LEDs-by-glowingkitty/GlowLight/images/glowlight_esp32_s3.jpg

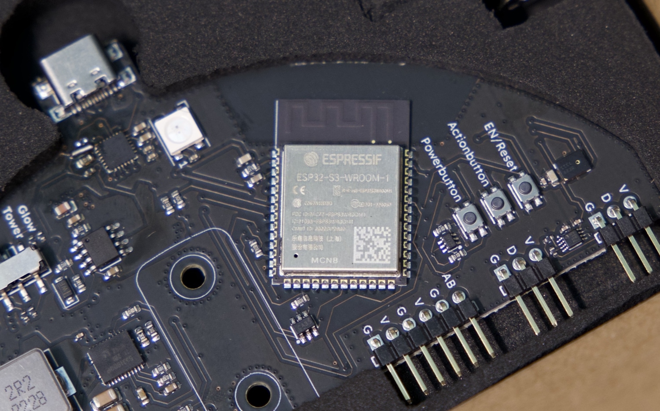
images/glowlight_esp32_s3.jpg
