LEDs-by-glowingkitty/GlowLight/images/glowlight_led_strips.jpg

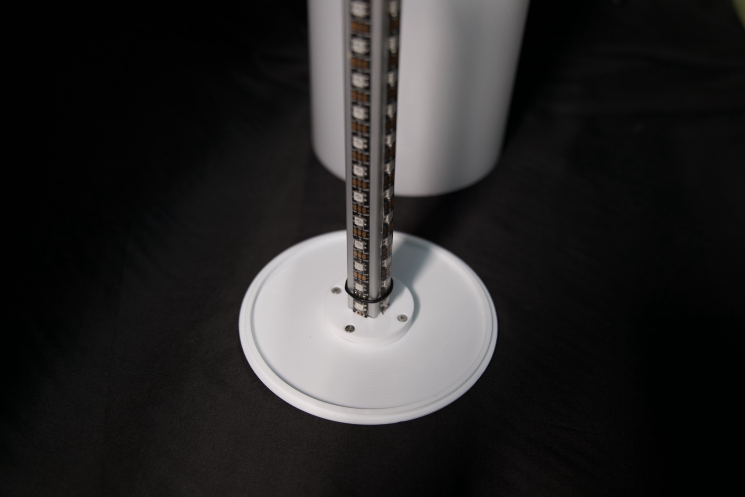
images/glowlight_led_strips.jpg
