LEDs-by-glowingkitty/GlowLight/images/glowlight_main_picture.jpg

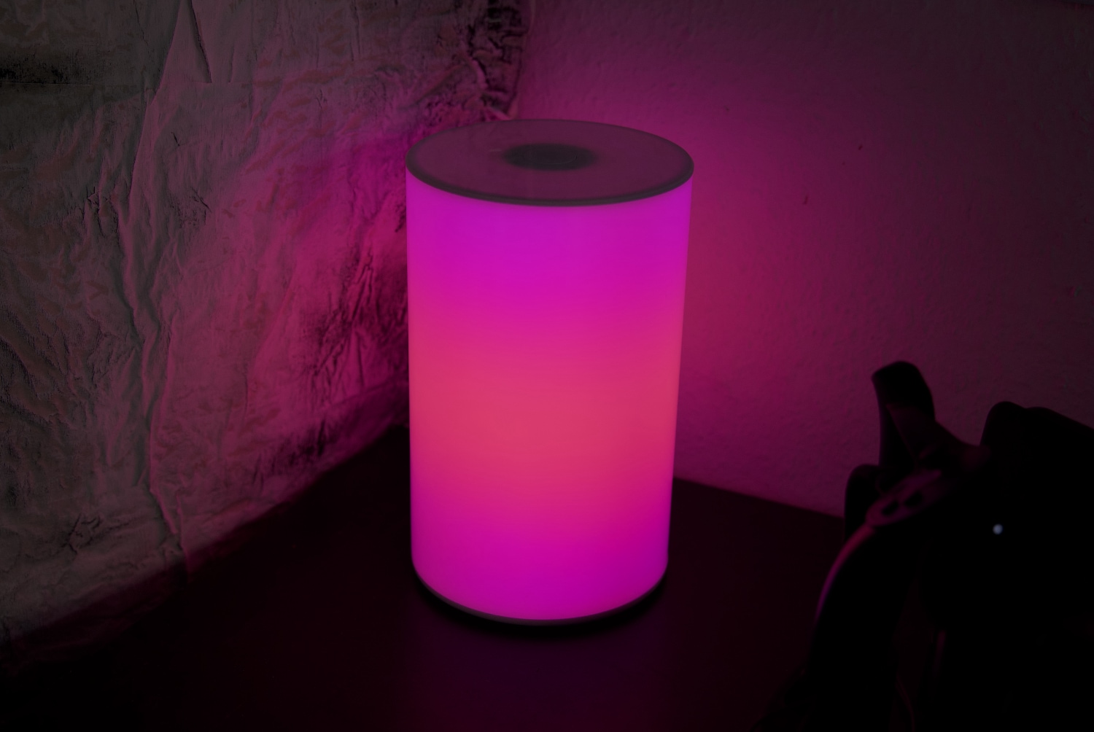
images/glowlight_main_picture.jpg
