LEDs-by-glowingkitty/GlowLight/images/glowlight_pcb.jpg

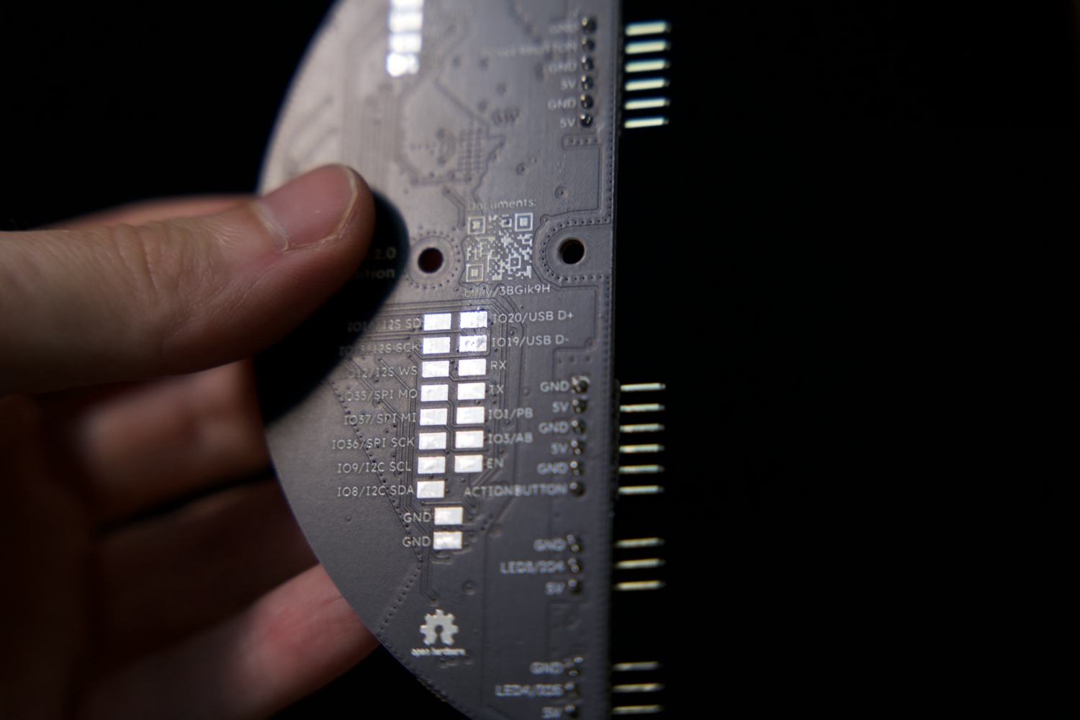
images/glowlight_pcb.jpg
