LEDs-by-glowingkitty/GlowLight/images/glowlight_white.jpg

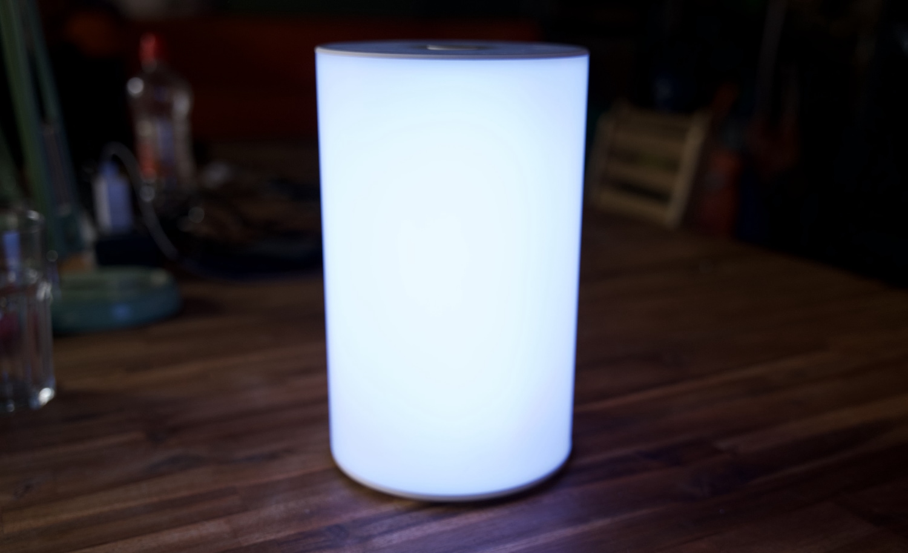
images/glowlight_white.jpg
