LEDs-by-glowingkitty/GlowLight/images/glowlightheader.jpg

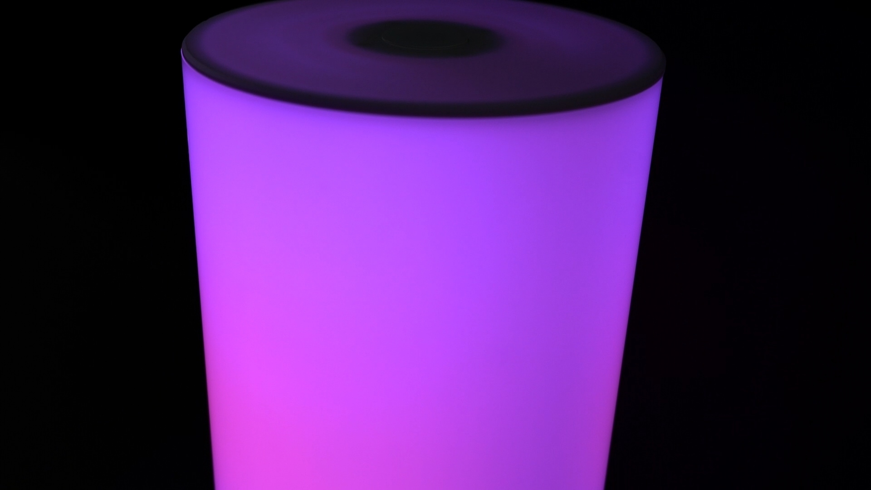
images/glowlightheader.jpg
