LEDs-by-glowingkitty/GlowLight/images/manyeffects.jpg

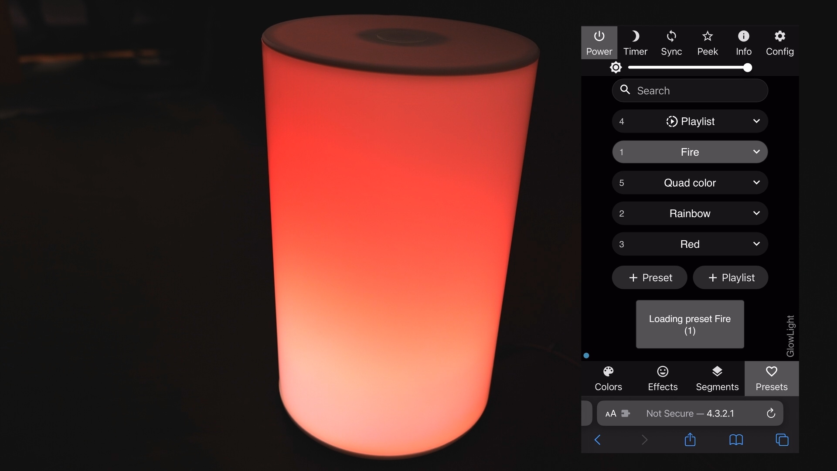
images/manyeffects.jpg
