LEDs-by-glowingkitty/GlowLight/PCB files/Button PCB/Button PCB.kicad_sch

## KiCad design PCB files/Button PCB/Button PCB.kicad_sch (2023-05-19)

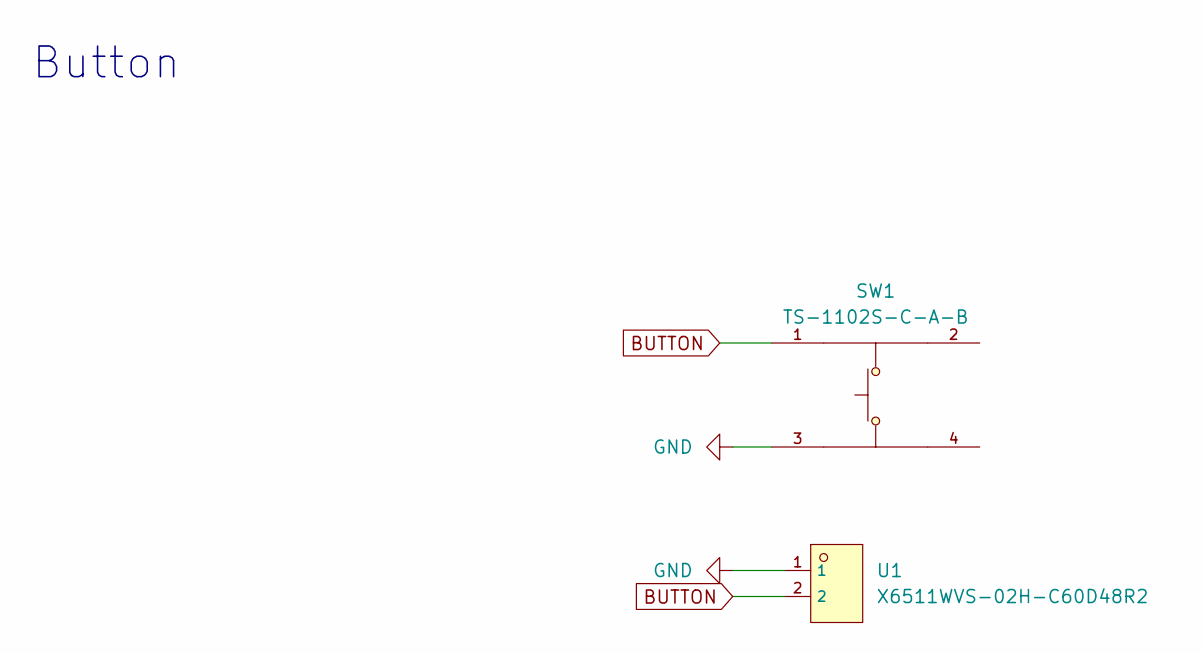
[picture p32: schematic Button PCB.kicad_sch]

Parts:
SW1: TS-1102S-C-A-B; KEY-SMD_4P-L6.0-W6.0-P4.50-LS8.6; LCSC # C381038
U1: X6511WVS-02H-C60D48R2; HDR-SMD_2P-P2.54_XKB_X6511WVS-02H-C60D48R2; LCSC C2883759

Connections:
BUTTON: SW1.1, U1.2
GND: SW1.3, U1.1

Notes on the sheet:
Button
