LEDs-by-glowingkitty/GlowLight/PCB files/MainPCB/MainPCB.kicad_sch

## KiCad design PCB files/MainPCB/MainPCB.kicad_sch (2023-12-09, an earlier design)

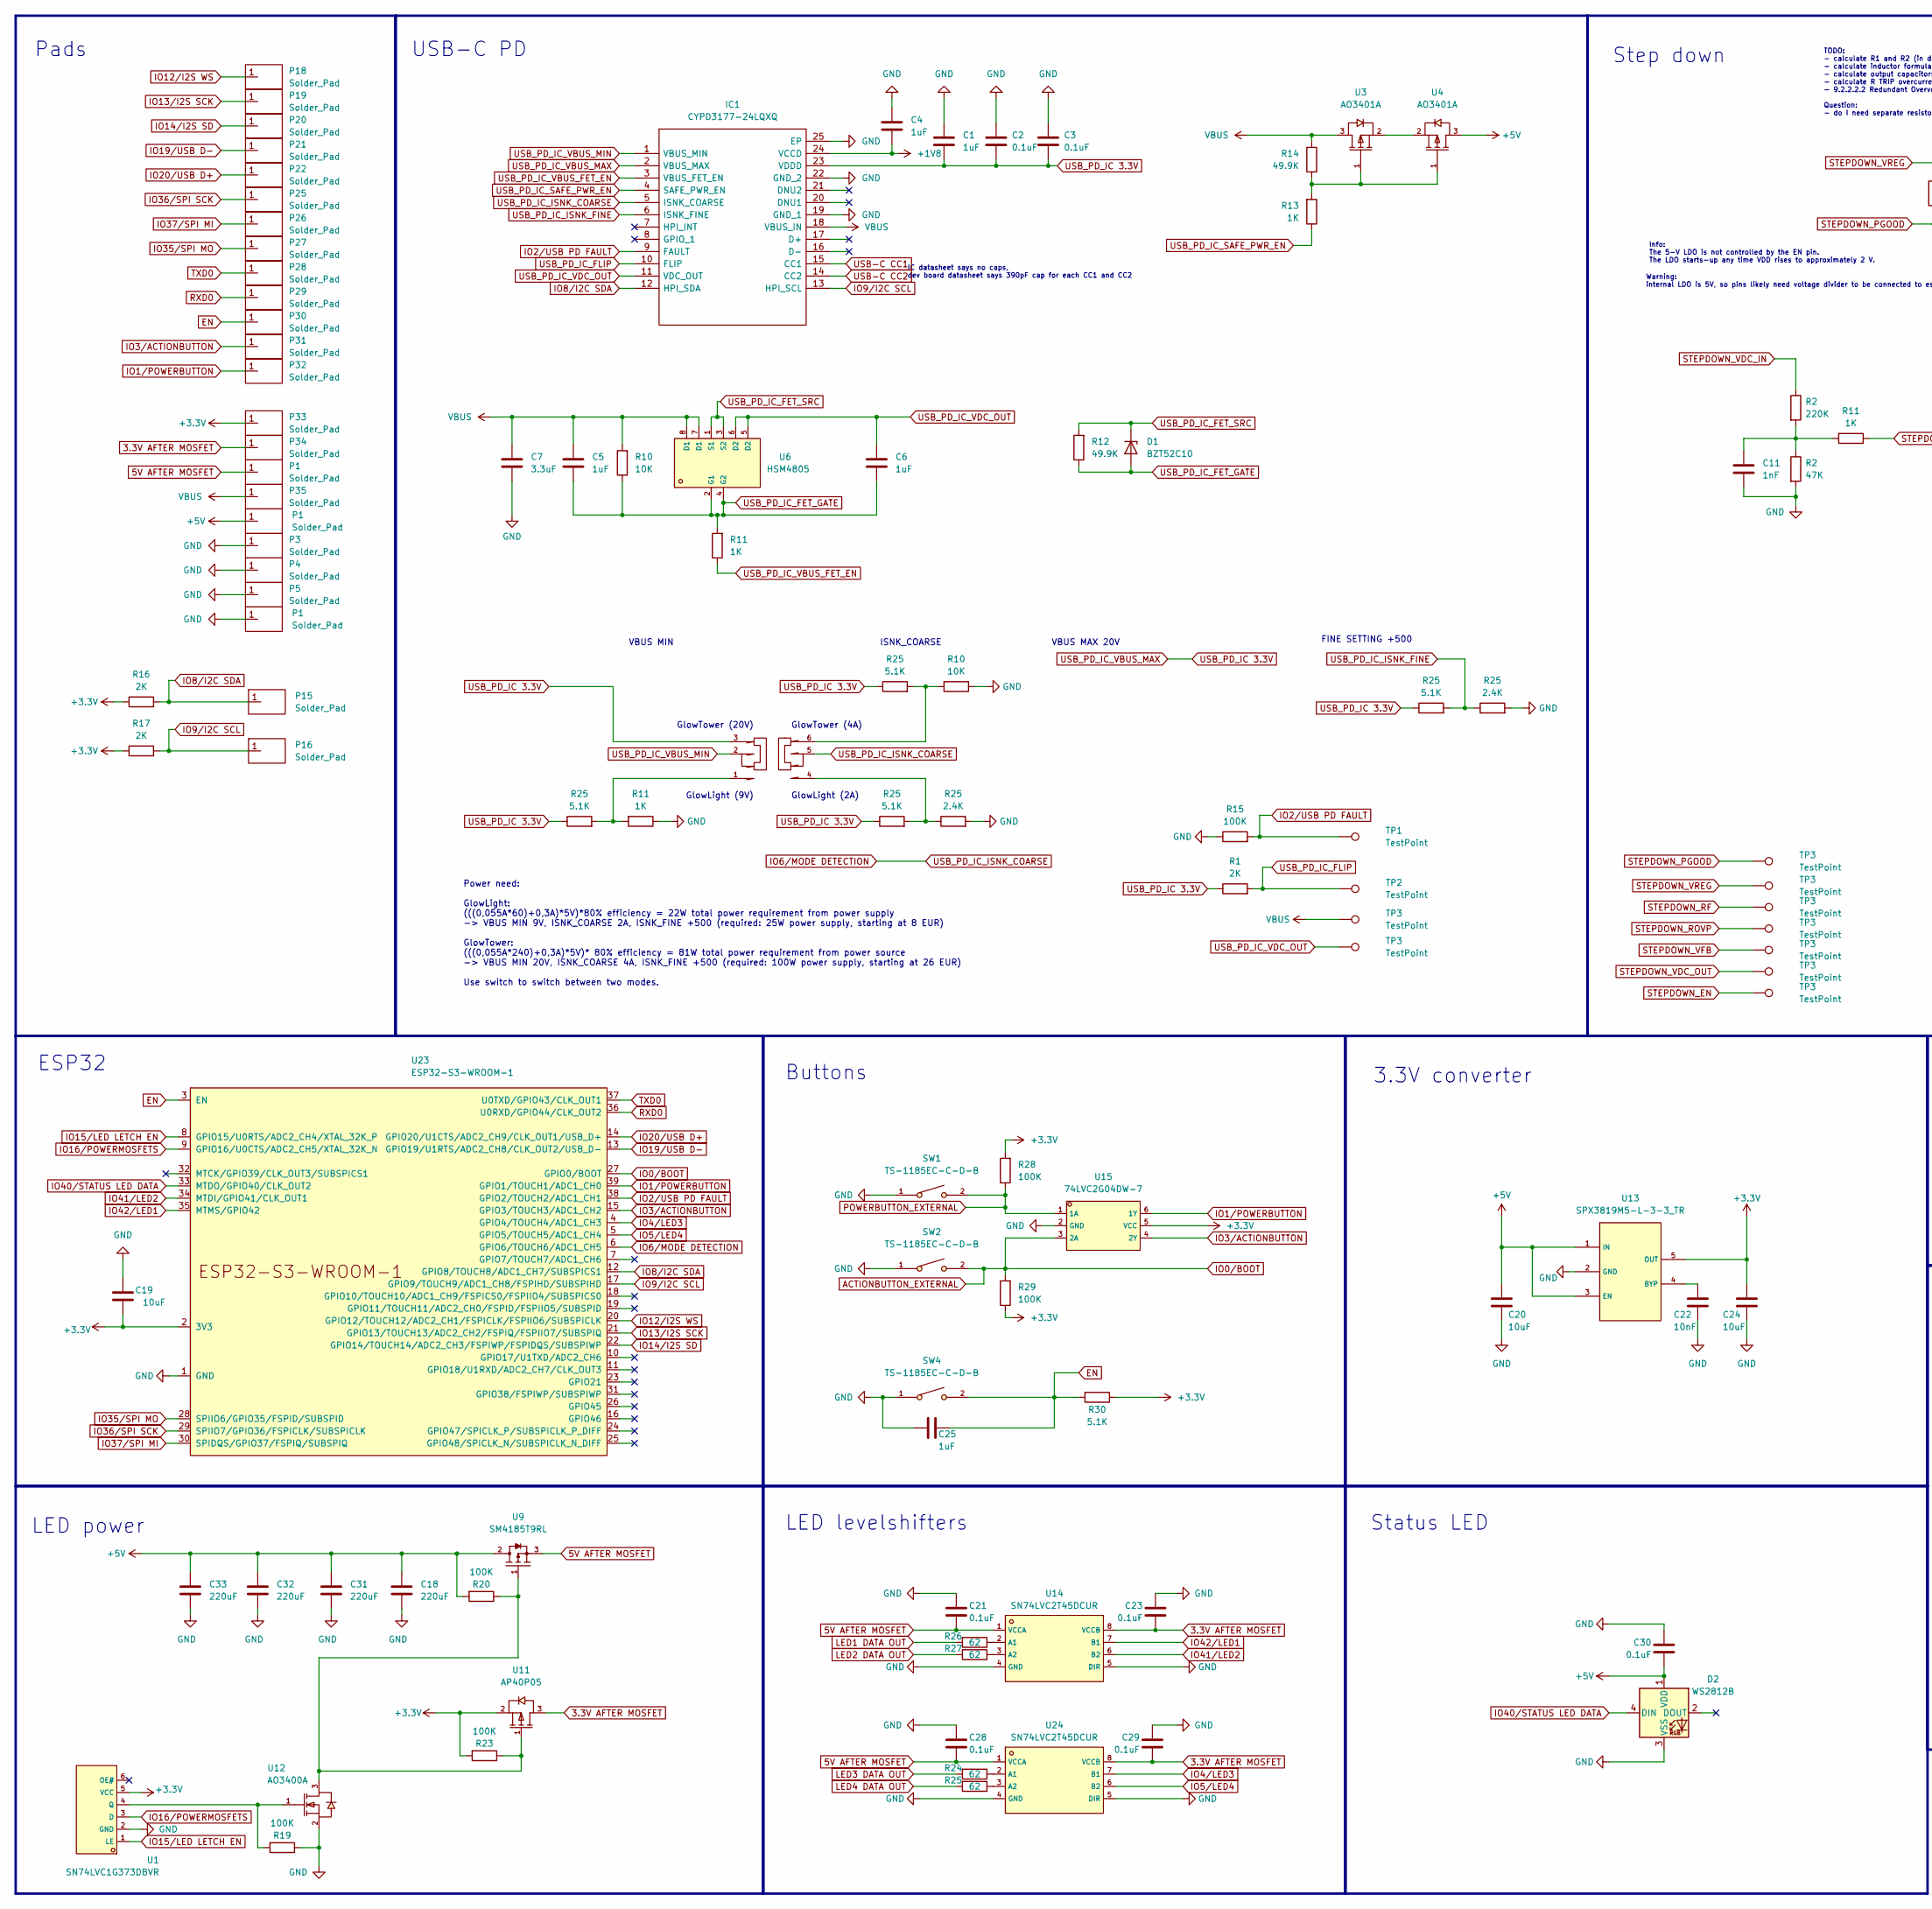
[picture p33: schematic MainPCB.kicad_sch, part in row 1, column 1]

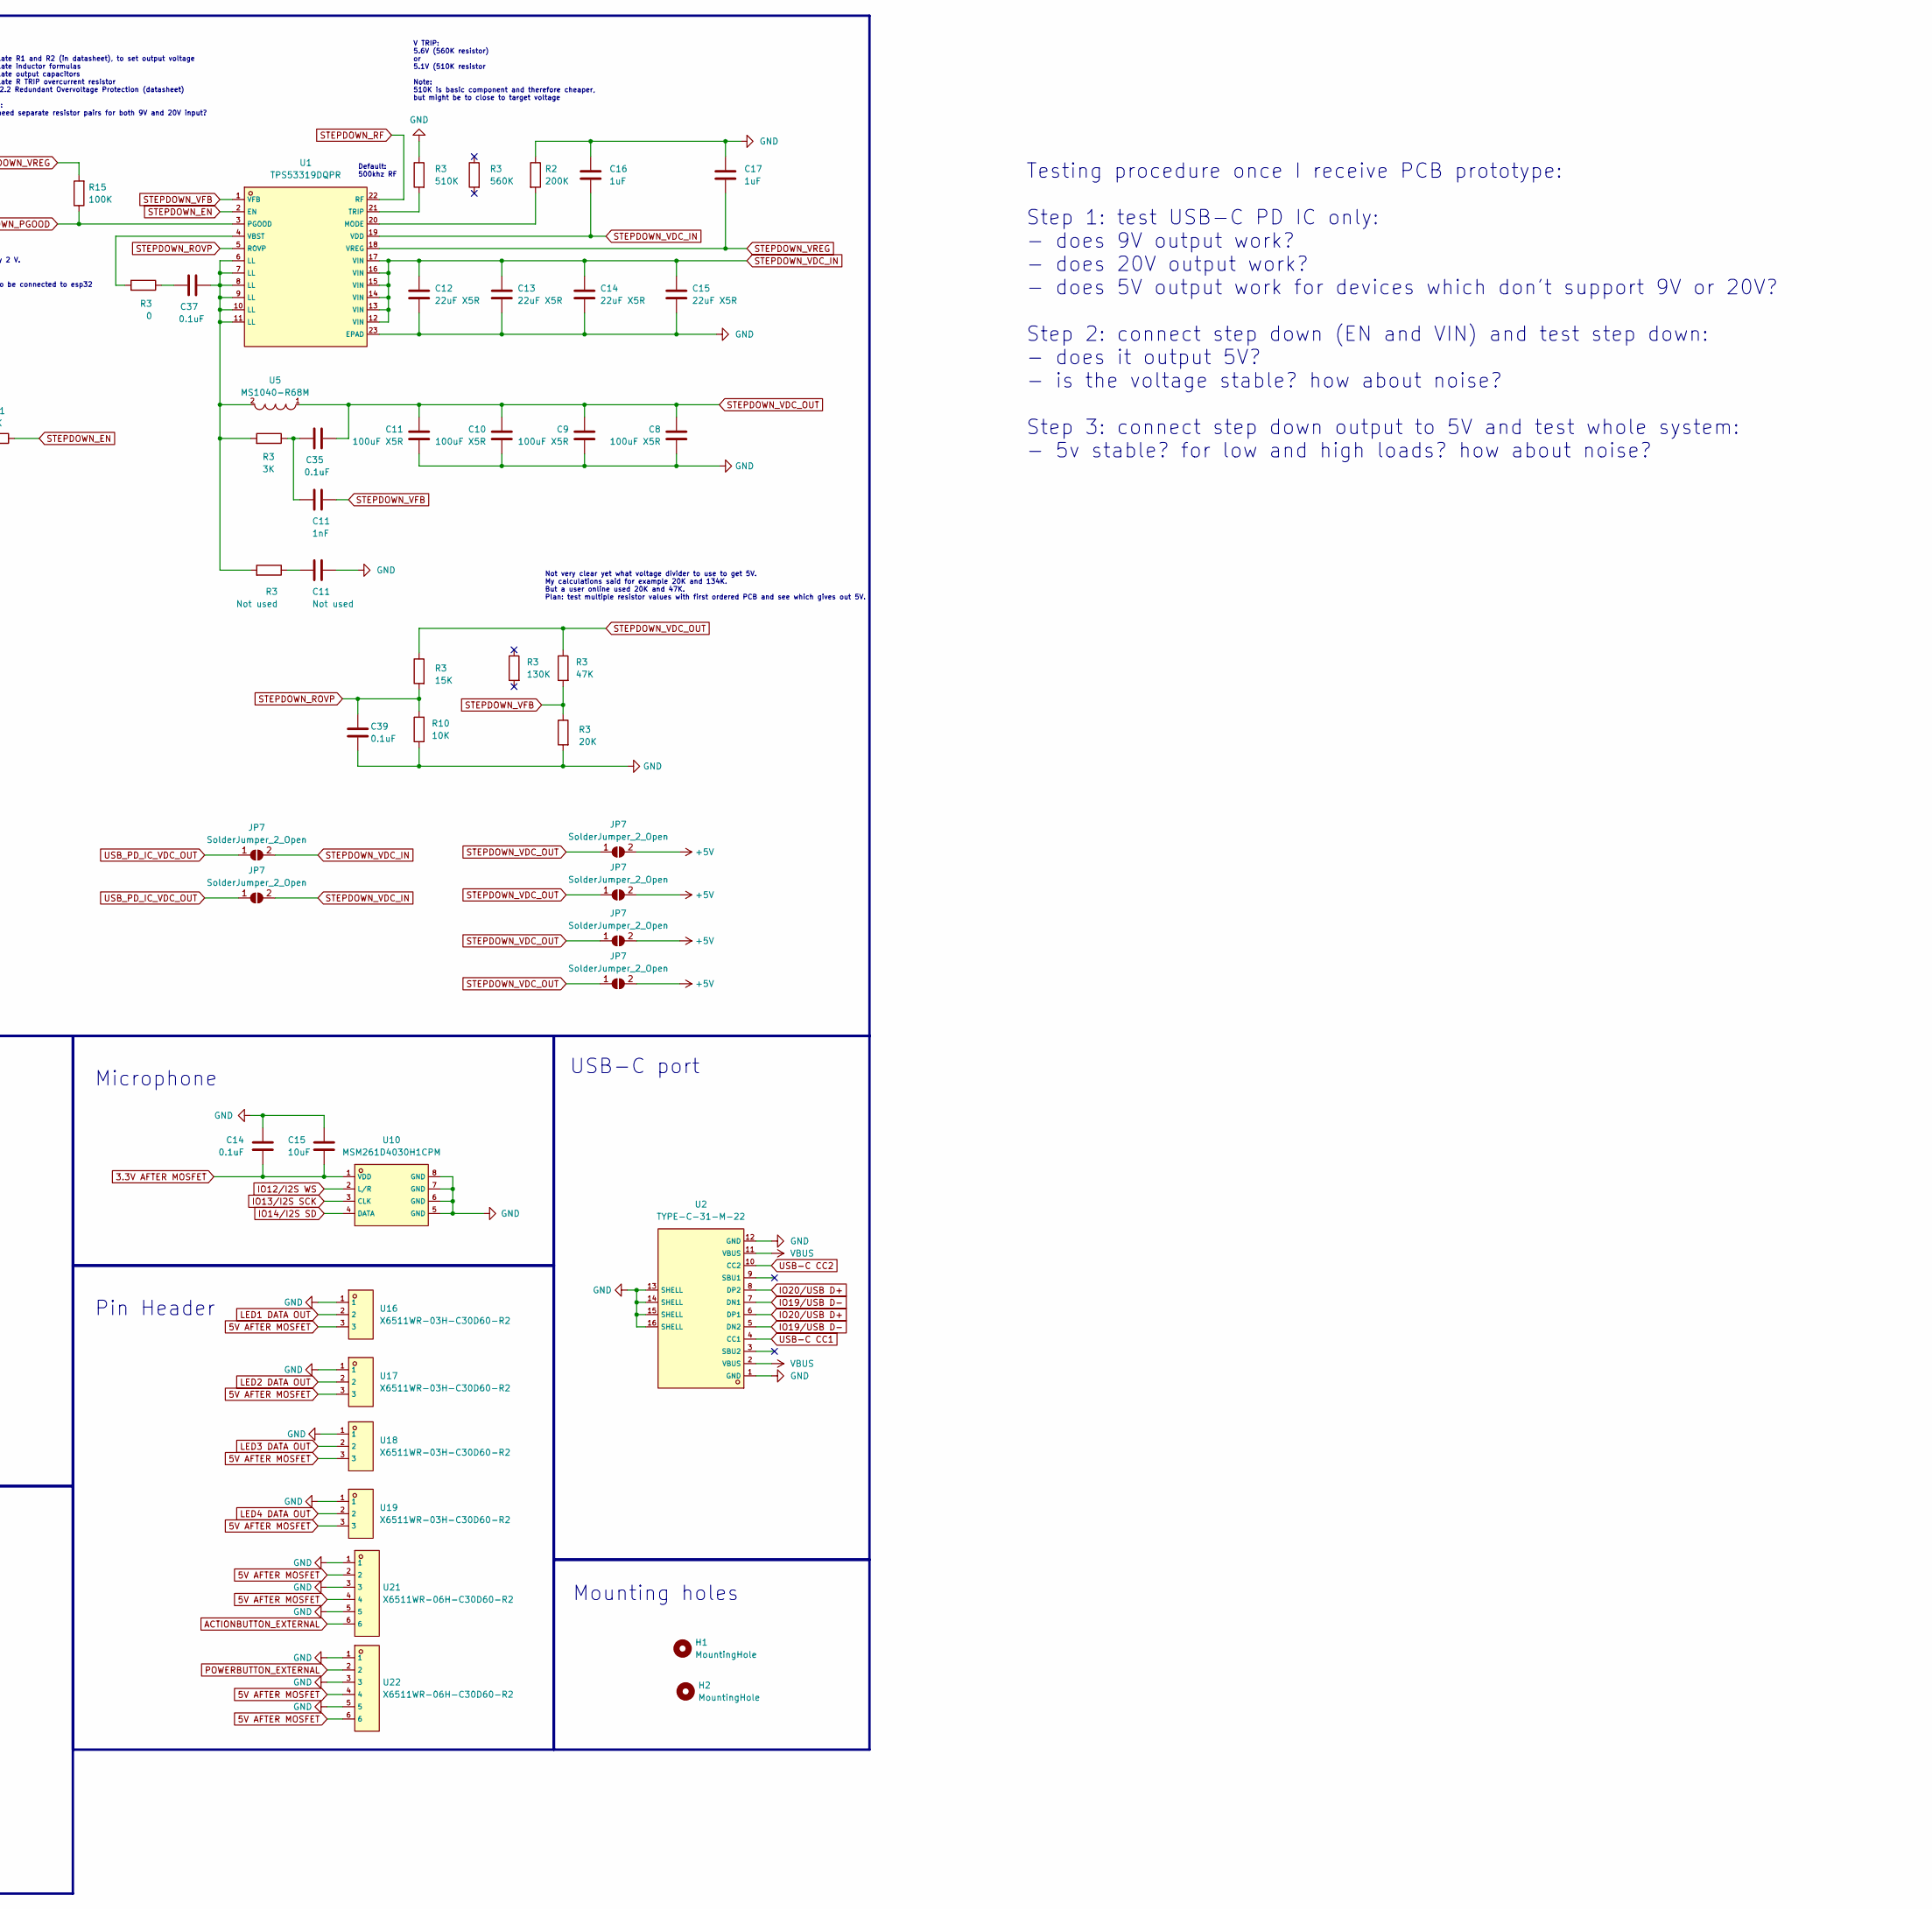
[picture p34: schematic MainPCB.kicad_sch, part in row 1, column 2]

Parts:
C1, C4, C5, C6, C16, C17, C25: 1uF; C_0603_1608Metric; LCSC # C15849
C2, C3, C14, C21, C23, C28, C29, C30, C35, C37, C39: 0.1uF; C_0402_1005Metric; LCSC # C307331
C7: 3.3uF; C_0805_2012Metric; LCSC # C342775
C8, C9, C10: 100uF X5R; C_1206_3216Metric; LCSC # C15008
C11: 1nF; C_0402_1005Metric; LCSC # C1523
C12, C13: 22uF X5R; C_1206_3216Metric; LCSC # C12891
C15, C19, C20, C24: 10uF; C_0603_1608Metric; LCSC # C96446
C18, C31, C32, C33: 220uF; C_1206_3216Metric; LCSC # C412252
C22: 10nF; C_0402_1005Metric; LCSC # C15195
D1: BZT52C10; D_SOD-123F; LCSC # C2891778
D2: WS2812B; LED_WS2812B_PLCC4_5.0x5.0mm_P3.2mm; LCSC # C2843785
H1, H2: MountingHole; MountingHole_3.2mm_M3
IC1: CYPD3177-24LQXQ; RT9471_vias_in_pad; LCSC # C2959321
JP7: SolderJumper_2_Open; SolderJumper-2_P1.3mm_Open_RoundedPad1.0x1.5mm
P1, P3, P4, P5, P15, P16, P18, P19, P20, P21, P22, P25, P26, P27, P28, P29, P30, P31, P32, P33, P34, P35: Solder_Pad; Solder pad
R1, R16, R17: 2K; R_0603_1608Metric; LCSC # C22975
R2: 200K; R_0603_1608Metric; LCSC # C25811
R3: Not used; R_0603_1608Metric
R10: 10K; R_0603_1608Metric; LCSC # C25804
R11, R13: 1K; R_0603_1608Metric; LCSC # C21190
R12, R14: 49.9K; R_0603_1608Metric; LCSC # C23184
R15, R19, R20, R23, R28, R29: 100K; R_0603_1608Metric; LCSC # C25803
R24, R26, R27: 62; R_0402_1005Metric; LCSC # C4962
R25: 2.4K; R_0603_1608Metric; LCSC # C22940
R30: 5.1K; R_0603_1608Metric; LCSC # C23186
SW1, SW2, SW4: TS-1185EC-C-D-B; SW-SMD_4P-L3.7-W3.0-P1.50-LS4.7; LCSC # C318893
SW3: SK-3245S-L3-B; SW-SMD_SK-3245S-L3-B; LCSC # C405954
TP1, TP2, TP3: TestPoint; TestPoint_Pad_D1.5mm
U1: TPS53319DQPR; LSON-CLIP-22_L6.0-W5.0-P0.50-BL-EP; LCSC # C181971
U2: TYPE-C-31-M-22; USB-C-SMD_TYPE-C-31-M-22; LCSC # C530612
U3, U4: AO3401A; SOT-23_L2.9-W1.3-P1.90-LS2.4-BR; LCSC # C15127
U5: MS1040-R68M; IND-SMD_L11.5-W10.0_MCF-1050; LCSC # C380043
U6: HSM4805; SOP-8_L4.9-W3.9-P1.27-LS6.0-BL; LCSC # C700973
U9: SM4185T9RL; TO-252-2_L6.6-W6.1-P4.57-LS10.1-BL-1; LCSC # C5143535
U10: MSM261D4030H1CPM; MIC-SMD_8P-L4.0-W3.0_ZTS6231; LCSC # C966942
U11: AP40P05; SOT-23-3_L2.9-W1.3-P1.90-LS2.4-BR; LCSC # C2886385
U12: AO3400A; SOT-23-3_L2.9-W1.6-P1.90-LS2.8-BR; LCSC # C20917
U13: SPX3819M5-L-3-3_TR; SOT-23-5_L3.0-W1.7-P0.95-LS2.8-BR; LCSC # C9055
U14, U24: SN74LVC2T45DCUR; VSSOP-8_L2.4-W2.1-P0.50-LS3.2-BR; LCSC # C15741
U15: 74LVC2G04DW-7; SOT-363_L2.0-W1.3-P0.65-LS2.1-BR; LCSC # C69053
U16, U17, U18, U19: X6511WR-03H-C30D60-R2; HDR-TH_3P-P2.54-H-M-W10.4; LCSC # C706866
U21, U22: X6511WR-06H-C30D60-R2; HDR-TH_6P-P2.54-H-M-W10.4; LCSC # C706869
U23: ESP32-S3-WROOM-1; LCSC # C2913197

Connections:
3.3V AFTER MOSFET: C14.2, C15.2, C23.2, C29.2, P34.1, U10.1 (VDD), U11.3 (D), U14.8 (VCCB), U24.8 (VCCB)
5V AFTER MOSFET: C21.2, C28.2, P1.1, U9.3 (S), U14.1 (VCCA), U16.3, U17.3, U18.3, U19.3, U21.2, U21.4, U22.4, U22.6, U24.1 (VCCA)
+1V8: C4.2, IC1.24 (VCCD)
+3.3V: C19.2, C24.2, P33.1, R16.1, R17.1, R23.2, R28.2, R29.1, R30.1, U1.5 (VCC), U11.2 (S), U13.5 (OUT), U15.5 (VCC), U23.2 (3V3)
+5V: C18.1, C20.2, C30.2, C31.1, C32.1, C33.1, D2.1 (VDD), JP7.2 (B), P1.1, R20.2, U4.3 (D), U9.2 (D), U13.1 (IN), U13.3 (EN)
ACTIONBUTTON_EXTERNAL: R29.2, SW2.2, U15.3 (2A), U21.6, U23.27 (GPIO0/BOOT)
EN: C25.2, P30.1, R30.2, SW4.2, U23.3 (EN)
GND: C1.1, C2.1, C3.1, C4.1, C7.1, C8.2, C9.2, C10.2, C11.1, C11.2, C12.2, C13.2, C14.1, C14.2, C15.1, C15.2, C16.1, C17.1, C18.2, C19.1, C20.1, C21.1, C22.1, C23.1, C24.1, C25.1, C28.1, C29.1, C30.1, C31.2, C32.2, C33.2, C39.2, D2.3 (VSS), IC1.19 (GND_1), IC1.22 (GND_2), IC1.25 (EP), P1.1, P3.1, P4.1, P5.1, R2.1, R2.2, R3.1, R3.2, R10.1, R11.1, R15.1, R19.1, R25.2, SW1.1, SW2.1, SW4.1, U1.2 (GND), U1.23 (EPAD), U2.1 (GND), U2.12 (GND), U2.13 (SHELL), U2.14 (SHELL), U2.15 (SHELL), U2.16 (SHELL), U10.5 (GND), U10.6 (GND), U10.7 (GND), U10.8 (GND), U12.2 (S), U13.2 (GND), U14.4 (GND), U14.5 (DIR), U15.2 (GND), U16.1, U17.1, U18.1, U19.1, U21.1, U21.3, U21.5, U22.1, U22.3, U22.5, U23.1 (GND), U23.40 (GND), U23.41 (GND), U24.4 (GND), U24.5 (DIR)
IO1/POWERBUTTON: P32.1, U15.6 (1Y), U23.39 (GPIO1/TOUCH1/ADC1_CH0)
IO2/USB PD FAULT: IC1.9 (FAULT), R15.2, TP1.1, U23.38 (GPIO2/TOUCH2/ADC1_CH1)
IO3/ACTIONBUTTON: P31.1, U15.4 (2Y), U23.15 (GPIO3/TOUCH3/ADC1_CH2)
IO4/LED3: U23.4 (GPIO4/TOUCH4/ADC1_CH3), U24.7 (B1)
IO5/LED4: U23.5 (GPIO5/TOUCH5/ADC1_CH4), U24.6 (B2)
IO6/MODE DETECTION: IC1.5 (ISNK_COARSE), SW3.5, U23.6 (GPIO6/TOUCH6/ADC1_CH5)
IO8/I2C SDA: IC1.12 (HPI_SDA), P15.1, R16.2, U23.12 (GPIO8/TOUCH8/ADC1_CH7/SUBSPICS1)
IO9/I2C SCL: IC1.13 (HPI_SCL), P16.1, R17.2, U23.17 (GPIO9/TOUCH9/ADC1_CH8/FSPIHD/SUBSPIHD)
IO12/I2S WS: P18.1, U10.2 (L/R), U23.20 (GPIO12/TOUCH12/ADC2_CH1/FSPICLK/FSPIIO6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)
IO13/I2S SCK: P19.1, U10.3 (CLK), U23.21 (GPIO13/TOUCH13/ADC2_CH2/FSPIQ/FSPIIO7/S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)
IO14/I2S SD: P20.1, U10.4 (DATA), U23.22 (GPIO14/TOUCH14/ADC2_CH3/FSPIWP/FSPIDQS/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)
IO15/LED LETCH EN: U1.1 (LE), U23.8 (GPIO15/U0RTS/ADC2_CH4/XTAL_32K_P)
IO16/POWERMOSFETS: U1.3 (D), U23.9 (GPIO16/U0CTS/ADC2_CH5/XTAL_32K_N)
IO19/USB D-: P21.1, U2.5 (DN2), U2.7 (DN1), U23.13 (GPIO19/U1RTS/ADC2_CH8/CLK_OUT2/USB_D-)
IO20/USB D+: P22.1, U2.6 (DP1), U2.8 (DP2), U23.14 (GPIO20/U1CTS/ADC2_CH9/CLK_OUT1/USB_D+)
IO35/SPI MO: P27.1, U23.28 (SPIIO6/GPIO35/FSPID/SUBSPID)
IO36/SPI SCK: P25.1, U23.29 (SPIIO7/GPIO36/FSPICLK/SUBSPICLK)
IO37/SPI MI: P26.1, U23.30 (SPIDQS/GPIO37/FSPIQ/SUBSPIQ)
IO40/STATUS LED DATA: D2.4 (DIN), U23.33 (MTDO/GPIO40/CLK_OUT2)
IO41/LED2: U14.6 (B2), U23.34 (MTDI/GPIO41/CLK_OUT1)
IO42/LED1: U14.7 (B1), U23.35 (MTMS/GPIO42)
LED1 DATA OUT: R26.2, U16.2
LED2 DATA OUT: R27.2, U17.2
LED3 DATA OUT: R24.2, U18.2
LED4 DATA OUT: R25.2, U19.2
unnamed: C11.1, R2.1, R2.2, R11.2
unnamed: C11.2, C35.1, R3.1
unnamed: C22.2, U13.4 (BYP)
unnamed: C37.1, R3.1
unnamed: C37.2, R3.2, U1.6 (OE#), U1.7 (LL), U1.8 (LL), U1.9 (LL), U1.10 (LL), U1.11 (LL), U5.2
unnamed: R2.2, U1.20 (MODE)
unnamed: R3.2, U1.4 (Q), U1.21 (TRIP)
unnamed: R10.2, R25.2, SW3.6
unnamed: R11.2, R25.2, SW3.1
unnamed: R13.2, R14.1, U3.1 (G), U4.1 (G)
unnamed: R19.2, U1.4 (Q), U12.1 (G)
unnamed: R20.1, R23.1, U9.1 (G), U11.1 (G), U12.3 (D)
unnamed: R24.1, U24.2 (A1)
unnamed: R25.1, R25.2, SW3.4, U24.3 (A2)
unnamed: R26.1, U14.2 (A1)
unnamed: R27.1, U14.3 (A2)
unnamed: U3.2 (S), U4.2 (S)
POWERBUTTON_EXTERNAL: R28.1, SW1.2, U15.1 (1A), U22.2
RXD0: P29.1, U23.36 (U0RXD/GPIO44/CLK_OUT2)
STEPDOWN_EN: R11.1, TP3.1, U1.2 (GND)
STEPDOWN_PGOOD: R15.1, TP3.1, U1.3 (D)
STEPDOWN_RF: TP3.1, U1.22 (RF)
STEPDOWN_ROVP: C39.1, R3.2, R10.2, TP3.1, U1.5 (VCC)
STEPDOWN_VDC_IN: C12.1, C13.1, C14.1, C15.1, C16.2, JP7.2 (B), R2.1, U1.12 (VIN), U1.13 (VIN), U1.14 (VIN), U1.15 (VIN), U1.16 (VIN), U1.17 (VIN), U1.19 (VDD)
STEPDOWN_VDC_OUT: C8.1, C9.1, C10.1, C11.1, C35.2, JP7.1 (A), R3.1, TP3.1, U5.1
STEPDOWN_VFB: C11.1, R3.1, R3.2, TP3.1, U1.1 (LE)
STEPDOWN_VREG: C17.2, R15.2, TP3.1, U1.18 (VREG)
TXD0: P28.1, U23.37 (U0TXD/GPIO43/CLK_OUT1)
USB-C CC1: IC1.15 (CC1), U2.4 (CC1)
USB-C CC2: IC1.14 (CC2), U2.10 (CC2)
USB_PD_IC 3.3V: C1.2, C2.2, C3.2, IC1.2 (VBUS_MAX), IC1.23 (VDDD), R1.1, R25.1, SW3.3
USB_PD_IC_FET_GATE: C5.2, C6.2, D1.2 (A), R10.1, R11.2, R12.1, U6.2 (G1), U6.4 (G2)
USB_PD_IC_FET_SRC: D1.1 (K), R12.2, U6.1 (S1), U6.3 (S2)
USB_PD_IC_FLIP: IC1.10 (FLIP), R1.2, TP2.1
USB_PD_IC_ISNK_FINE: IC1.6 (ISNK_FINE), R25.1, R25.2
USB_PD_IC_SAFE_PWR_EN: IC1.4 (SAFE_PWR_EN), R13.1
USB_PD_IC_VBUS_FET_EN: IC1.3 (VBUS_FET_EN), R11.1
USB_PD_IC_VBUS_MIN: IC1.1 (VBUS_MIN), SW3.2
USB_PD_IC_VDC_OUT: C6.1, IC1.11 (VDC_OUT), JP7.1 (A), TP3.1, U6.5 (D2), U6.6 (D2)
VBUS: C5.1, C7.2, IC1.18 (VBUS_IN), P35.1, R10.2, R14.2, TP3.1, U2.2 (VBUS), U2.11 (VBUS), U3.3 (D), U6.7 (D1), U6.8 (D1)

Notes on the sheet:
Status LED
Info: The 5-V LDO is not controlled by the EN pin. The LDO starts-up any time VDD rises to approximately 2 V.
LED levelshifters
Buttons
3.3V converter
USB-C port
Default: 500khz RF
Testing procedure once I receive PCB prototype: Step 1: test USB-C PD IC only: - does 9V output work? - does 20V output work? - does 5V output work for devices which don't support 9V or 20V? Step 2: connect step down (EN and VIN) and test step down: - does it output 5V? - is the voltage stable? how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
VBUS MAX 20V
ESP32
Not very clear yet what voltage divider to use to get 5V. My calculations said for example 20K and 134K. But a user online used 20K and 47K. Plan: test multiple resistor values with first ordered PCB and see which gives out 5V.
GlowTower (4A)
GlowLight (9V)
Pin Header
IC datasheet says no caps, dev board datasheet says 390pF cap for each CC1 and CC2
LED power
VBUS MIN
USB-C PD
GlowTower (20V)
Step down
FINE SETTING +500
TODO: - calculate R1 and R2 (in datasheet), to set output voltage - calculate inductor formulas - calculate output capacitors - calculate R TRIP overcurrent resistor - 9.2.2.2.2 Redundant Overvoltage Protection (datasheet) Question: - do I need separate resistor pairs for both 9V and 20V input?
Pads
Power need: GlowLight: (((0,055A*60)+0,3A)*5V)*80% efficiency = 22W total power requirement from power supply -> VBUS MIN 9V, ISNK_COARSE 2A, ISNK_FINE +500 (required: 25W power supply, starting at 8 EUR) GlowTower: (((0,055A*240)+0,3A)*5V)* 80% efficiency = 81W total power requirement from power s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
Microphone
V TRIP: 5.6V (560K resistor) or 5.1V (510K resistor Note: 510K is basic component and therefore cheaper, but might be to close to target voltage
ISNK_COARSE
Warning: internal LDO is 5V, so pins likely need voltage divider to be connected to esp32
Mounting holes
GlowLight (2A)
